plahutaT/FanController_HW_SW/h_files/main_menu.h

/* 
 * File:   main_menu.h
 * Author: tilen
 *
 * Created on April 9, 2023, 8:07 PM
 */

#ifndef MAIN_MENU_H
#define	MAIN_MENU_H

#include <stdint.h>
#include <stdio.h>
#include "LCD.h"
#include "button.h"

extern uint8_t Ref_temp;
extern volatile uint32_t multitaskTimer;
extern uint8_t Main_menu_F;
extern uint8_t Main_menu2_F;
extern uint8_t DC_fan_F;
extern uint8_t DC_fan_running_F;


uint32_t TicksM = 0;

void main_menu_func(void);
//void first_main_menu_func(void);
void display_menu (uint8_t flags);


#endif	/* MAIN_MENU_H */
