plahutaT/FanController_HW_SW/c_files/LCD_init.c

#include "LCD.h"


/* Initialize the global variables */
uint8_t LCD_display_control = LCD_CMD_DISPLAY_CONTROL;
uint8_t LCD_entry_mode      = LCD_CMD_ENTRY_MODE;


/**
 * Initializes the LCD\n
 * <u>LCD configured as:</u>\n
 * - Function set: 4-bit, 2-line, 5x8 dots\n
 * - Display: On\n
 * - Cursor display: Off\n
 * - Cursor blink: Off\n
 * - Cursor on write: Increment, no shift\n
 */
void LCD_init(){
    
    //---------- Pin configurations ----------
    LCD_RS_TRIS = 0; LCD_RS_LAT = 0;
    LCD_EN_TRIS = 0; LCD_EN_LAT = 0;
    LCD_D4_TRIS = 0; LCD_D4_LAT = 0;
    LCD_D5_TRIS = 0; LCD_D5_LAT = 0;
    LCD_D6_TRIS = 0; LCD_D6_LAT = 0;
    LCD_D7_TRIS = 0; LCD_D7_LAT = 0;
    
    //******************************************************************//
    //*** Sequence for "Initializing 4-bit interface" from datasheet ***//
    //******************************************************************//
    
    //---------- Wait for more than 40ms ----------
    __delay_ms(80);
    
    
    for (uint8_t i = 0; i < 6; i++) {
        
        //---------- Load 0b0011 in command mode ----------
        LCD_D7_LAT = 0; LCD_D6_LAT = 0; LCD_D5_LAT = 1; LCD_D4_LAT = 1;

        //---------- Send a clock pulse ----------
        LCD_pulse_clock();
        
        __delay_ms(5);
    
    }
    
    
    //---------- Load 0b0010 in command mode ----------
    LCD_D7_LAT = 0; LCD_D6_LAT = 0; LCD_D5_LAT = 1; LCD_D4_LAT = 0;
    
    //---------- Send a clock pulse ----------
    LCD_pulse_clock();
    
    __delay_ms(1);
    
    
    //---------- Configure important settings ----------
    LCD_write_command(LCD_CMD_FUNCTION_SET);  //Function Set(4-bit, 2 line, 5x8 dots)
    __delay_ms(1);
    LCD_write_command(LCD_display_control);   //Display On/Off Control(Display on, cursor off, blinking off)
    __delay_ms(1);
    LCD_write_command(LCD_entry_mode);        //Entry Mode Set(Increment, shift off)
    __delay_ms(1);
    LCD_clear();                              //Clear the display
 }
    
    
