plahutaT/FanController_HW_SW/c_files/ring_buffer.c

#include "ring_buffer.h"

void ring_buffer_push(ring_buffer *rb, uint8_t value){
   
    rb->buffer[rb->head] = value;
    rb->head++;

    // Avoid expensive modulo operation
    if (rb->head == rb->size) {
        rb->head = 0;
    }

    // If ring_buffer is full, remove oldest element
    if (rb->head == rb->tail) {
        rb->tail++;
    }
}

uint8_t ring_buffer_pop(ring_buffer *rb){
    
    const uint8_t data = rb->buffer[rb->tail];
    rb->tail++;

    // Avoid expensive modulo operation
    if (rb->tail == rb->size) {
        rb->tail = 0;
    }

    return data;

}


uint8_t ring_buffer_peek(const ring_buffer *rb){

    return rb->buffer[rb->tail];
    
}


uint8_t ring_buffer_full(const ring_buffer *rb){
    
    uint8_t idx_after_head = rb->head + 1;
    
    if(idx_after_head == rb->size){   
        idx_after_head = 0;
    }    
    
    return idx_after_head == rb->tail;
    
}
uint8_t ring_buffer_empty(const ring_buffer *rb){

    return rb->head == rb->tail;

}
